db-ok/SofleChocWireless/SofleChocWireless/PCB/SofleKeyboard.kicad_sch

## KiCad design SofleChocWireless/PCB/SofleKeyboard.kicad_sch (2023-11-16)

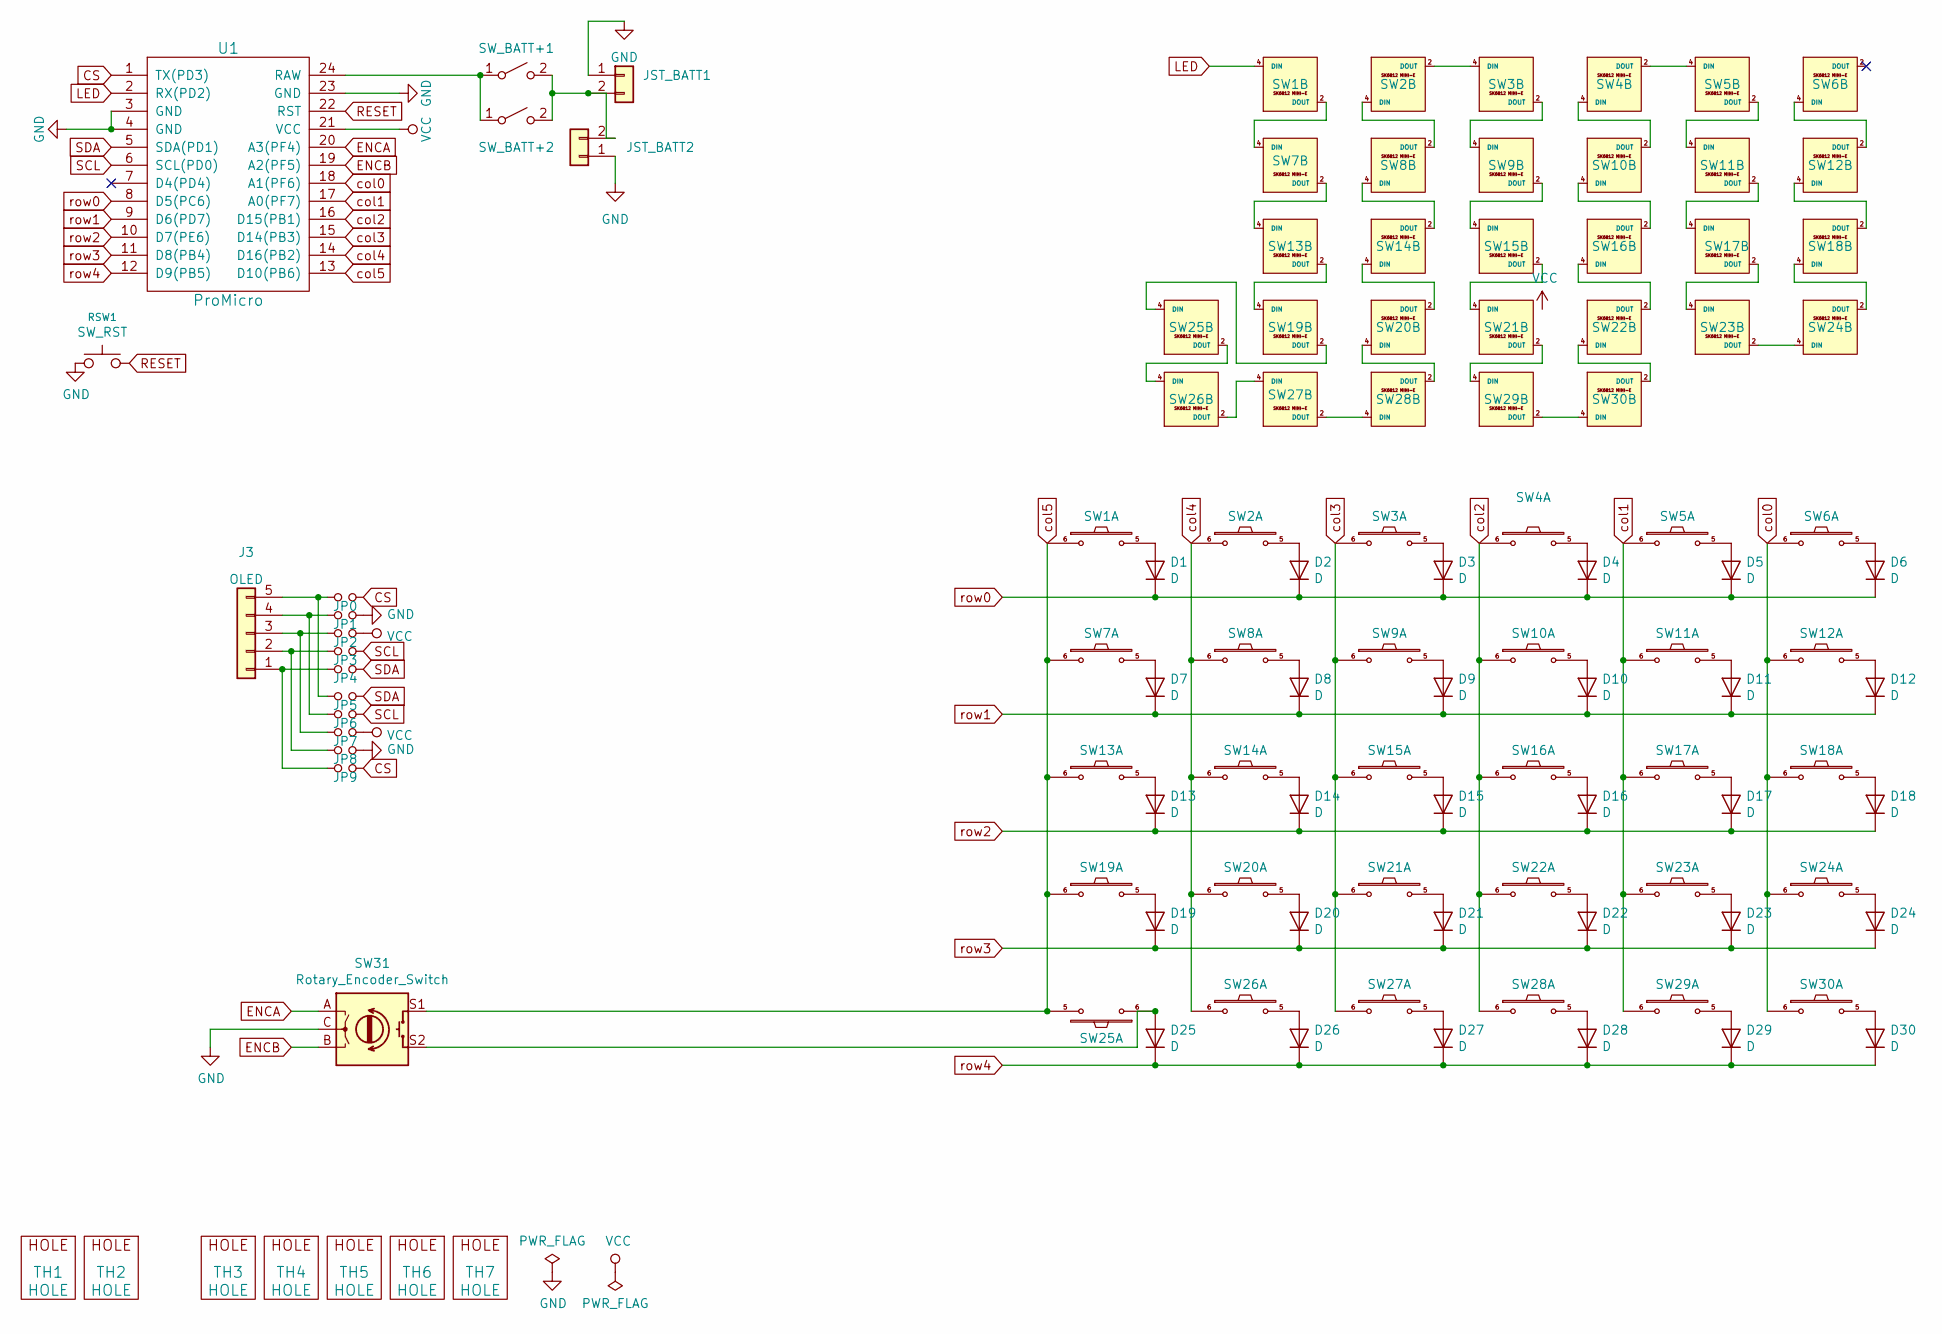
[picture p22: schematic SofleKeyboard.kicad_sch]

Parts:
D1, D2, D3, D4, D5, D6, D7, D8, D9, D10, D11, D12, D13, D14, D15, D16, D17, D18, D19, D20, D21, D22, D23, D24, D25, D26, D27, D28, D29, D30: D; crkbd-diode
J3: OLED; OLED_NICEVIEW_COMBO_HDR_5Pin
JP0, JP1, JP2, JP3, JP4, JP5, JP6, JP7, JP8, JP9: Jumper_NO_Small; Jumper_small
JST_BATT1, JST_BATT2: Conn_01x02; JST_PH_S2B-PH-K_1x02_P2.00mm_DoubleSided
RSW1: SW_RST; TACT_SWITCH_TVBP06
SW1, SW7, SW13, SW19: SW_PUSH_LED; Choc_Hotswap_SK6812MiniE_BiggerHSPads_Column1
SW2, SW3, SW4, SW5, SW6, SW8, SW9, SW10, SW11, SW12, SW14, SW15, SW16, SW17, SW18, SW20, SW21, SW22, SW23, SW24, SW26, SW27, SW28, SW29, SW30: SW_PUSH_LED; Choc_Hotswap_SK6812MiniE_BiggerHSPads
SW25: SW_PUSH_LED; Kailh-PG1350-1u-reversible-SK6812MiniE_MODIFIED
SW31: Rotary_Encoder_Switch; RotaryEncoder_Alps_EC11E-Switch_Vertical_H20mm-keebio_modif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
SW_BATT+1, SW_BATT+2: SW_SPST; SW_SPDT_PCM12
TH1, TH2: HOLE; M2_HOLE_PCB
TH3, TH4, TH5, TH6, TH7: HOLE; HOLE_M2_TH
U1: ProMicro

Connections:
CS: JP0.2, JP9.2, U1.1 (TX(PD3))
ENCA: SW31.A, U1.20 (A3(PF4))
ENCB: SW31.B, U1.19 (A2(PF5))
GND: JP1.2, JP8.2, JST_BATT1.1, JST_BATT2.1, RSW1.1, SW31.C, U1.3 (GND), U1.4 (GND), U1.23 (GND)
LED: SW1.4 (DIN), U1.2 (RX(PD2))
unnamed: D1.2 (A), SW1.5
unnamed: D2.2 (A), SW2.5
unnamed: D3.2 (A), SW3.5
unnamed: D4.2 (A), SW4.5
unnamed: D5.2 (A), SW5.5
unnamed: D6.2 (A), SW6.5
unnamed: D7.2 (A), SW7.5
unnamed: D8.2 (A), SW8.5
unnamed: D9.2 (A), SW9.5
unnamed: D10.2 (A), SW10.5
unnamed: D11.2 (A), SW11.5
unnamed: D12.2 (A), SW12.5
unnamed: D13.2 (A), SW13.5
unnamed: D14.2 (A), SW14.5
unnamed: D15.2 (A), SW15.5
unnamed: D16.2 (A), SW16.5
unnamed: D17.2 (A), SW17.5
unnamed: D18.2 (A), SW18.5
unnamed: D19.2 (A), SW19.5
unnamed: D20.2 (A), SW20.5
unnamed: D21.2 (A), SW21.5
unnamed: D22.2 (A), SW22.5
unnamed: D23.2 (A), SW23.5
unnamed: D24.2 (A), SW24.5
unnamed: D25.2 (A), SW25.6, SW31.S2
unnamed: D26.2 (A), SW26.5
unnamed: D27.2 (A), SW27.5
unnamed: D28.2 (A), SW28.5
unnamed: D29.2 (A), SW29.5
unnamed: D30.2 (A), SW30.5
unnamed: J3.1, JP4.1, JP9.1
unnamed: J3.2, JP3.1, JP8.1
unnamed: J3.3, JP2.1, JP7.1
unnamed: J3.4, JP1.1, JP6.1
unnamed: J3.5, JP0.1, JP5.1
unnamed: JST_BATT1.2, JST_BATT2.2, SW_BATT+1.2 (B), SW_BATT+2.2 (B)
unnamed: SW1.2 (DOUT), SW7.4 (DIN)
unnamed: SW2.2 (DOUT), SW3.4 (DIN)
unnamed: SW2.4 (DIN), SW8.2 (DOUT)
unnamed: SW3.2 (DOUT), SW9.4 (DIN)
unnamed: SW4.2 (DOUT), SW5.4 (DIN)
unnamed: SW4.4 (DIN), SW10.2 (DOUT)
unnamed: SW10.4 (DIN), SW16.2 (DOUT)
unnamed: SW11.2 (DOUT), SW17.4 (DIN)
unnamed: SW5.2 (DOUT), SW11.4 (DIN)
unnamed: SW6.4 (DIN), SW12.2 (DOUT)
unnamed: SW12.4 (DIN), SW18.2 (DOUT)
unnamed: SW13.2 (DOUT), SW19.4 (DIN)
unnamed: SW7.2 (DOUT), SW13.4 (DIN)
unnamed: SW8.4 (DIN), SW14.2 (DOUT)
unnamed: SW14.4 (DIN), SW20.2 (DOUT)
unnamed: SW15.2 (DOUT), SW21.4 (DIN)
unnamed: SW9.2 (DOUT), SW15.4 (DIN)
unnamed: SW16.4 (DIN), SW22.2 (DOUT)
unnamed: SW17.2 (DOUT), SW23.4 (DIN)
unnamed: SW18.4 (DIN), SW24.2 (DOUT)
unnamed: SW19.2 (DOUT), SW25.4 (DIN)
unnamed: SW20.4 (DIN), SW28.2 (DOUT)
unnamed: SW21.2 (DOUT), SW29.4 (DIN)
unnamed: SW22.4 (DIN), SW30.2 (DOUT)
unnamed: SW23.2 (DOUT), SW24.4 (DIN)
unnamed: SW25.2 (DOUT), SW26.4 (DIN)
unnamed: SW26.2 (DOUT), SW27.4 (DIN)
unnamed: SW27.2 (DOUT), SW28.4 (DIN)
unnamed: SW29.2 (DOUT), SW30.4 (DIN)
unnamed: SW_BATT+1.1 (A), SW_BATT+2.1 (A), U1.24 (RAW)
RESET: RSW1.2, U1.22 (RST)
SCL: JP3.2, JP6.2, U1.6 (SCL(PD0))
SDA: JP4.2, JP5.2, U1.5 (SDA(PD1))
VCC: JP2.2, JP7.2, SW21.1 (VDD), U1.21 (VCC)
col0: SW6.6, SW12.6, SW18.6, SW24.6, SW30.6, U1.18 (A1(PF6))
col1: SW5.6, SW11.6, SW17.6, SW23.6, SW29.6, U1.17 (A0(PF7))
col2: SW4.6, SW10.6, SW16.6, SW22.6, SW28.6, U1.16 (D15(PB1))
col3: SW3.6, SW9.6, SW15.6, SW21.6, SW27.6, U1.15 (D14(PB3))
col4: SW2.6, SW8.6, SW14.6, SW20.6, SW26.6, U1.14 (D16(PB2))
col5: SW1.6, SW7.6, SW13.6, SW19.6, SW25.5, SW31.S1, U1.13 (D10(PB6))
row0: D1.1 (K), D2.1 (K), D3.1 (K), D4.1 (K), D5.1 (K), D6.1 (K), U1.8 (D5(PC6))
row1: D7.1 (K), D8.1 (K), D9.1 (K), D10.1 (K), D11.1 (K), D12.1 (K), U1.9 (D6(PD7))
row2: D13.1 (K), D14.1 (K), D15.1 (K), D16.1 (K), D17.1 (K), D18.1 (K), U1.10 (D7(PE6))
row3: D19.1 (K), D20.1 (K), D21.1 (K), D22.1 (K), D23.1 (K), D24.1 (K), U1.11 (D8(PB4))
row4: D25.1 (K), D26.1 (K), D27.1 (K), D28.1 (K), D29.1 (K), D30.1 (K), U1.12 (D9(PB5))
